clvLabs/gas-oil-tank-level/src/ui/states/config.h

#pragma once

#include "Arduino.h"
#include <NewPing.h>
#include "U8glib.h"
#include "../../config.h"
#include "../../utils/u8gutils.h"
#include "../../utils/battery.h"
#include "../../utils/utils.h"
#include "../uistate.h"

namespace ui
{

    class Config : public UIState
    {
        int currentField;
        char valueStr[20];

    public:
        Config(UIMgr *pUI);

        void setup();
        void loop();
        void onEnter();
        void beforePaint();
        void paint();
        bool afterPaint();

    private:
        void updateValue(unsigned int *pValue, unsigned int pMin, unsigned int pMax);
    };

} // namespace ui
